LaskaKit/LED_Czech_Map/img/9.jpg

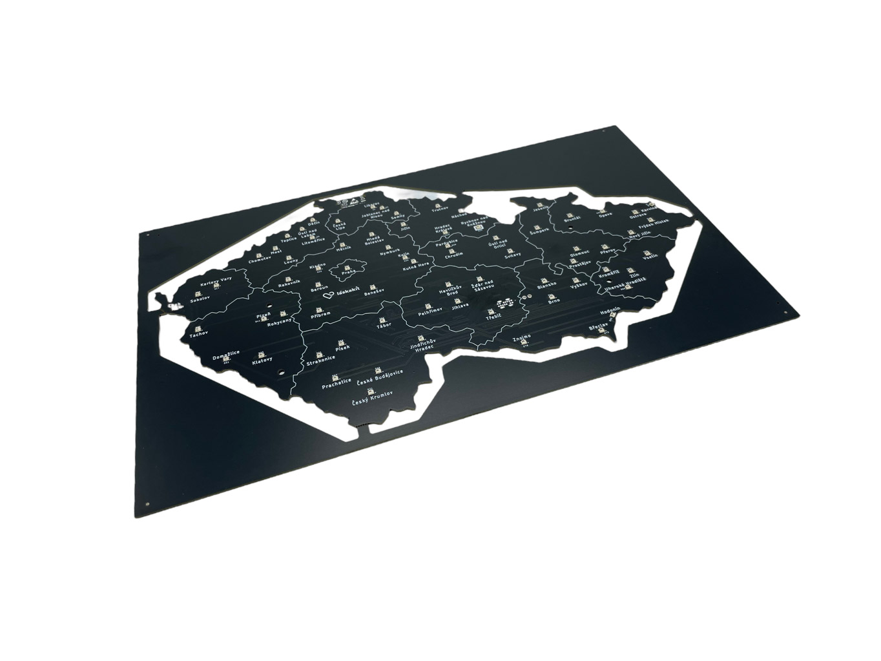
img/9.jpg
