LaskaKit/LED_Czech_Map/img/11.jpg

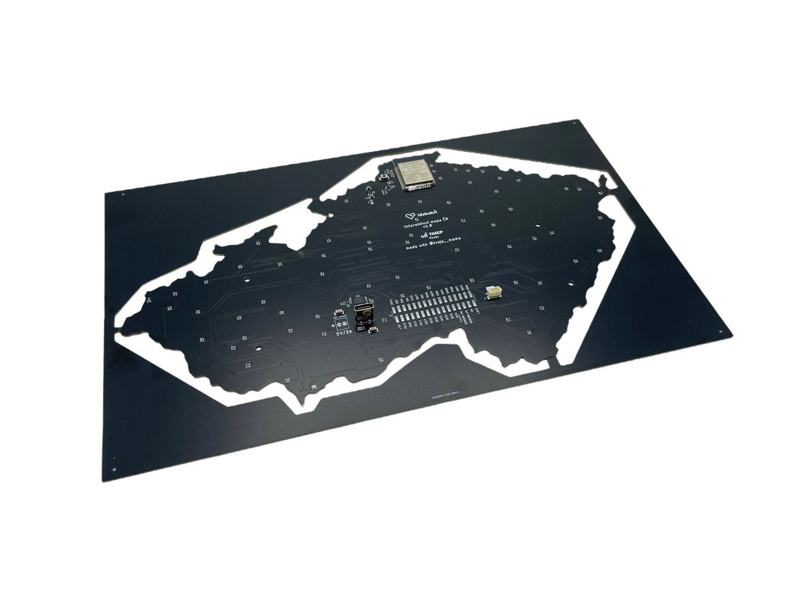
img/11.jpg
