LaskaKit/LED_Czech_Map/SW/Hra_Zachran_Mesto/laskakit_mapa_kontrola_otazek.png

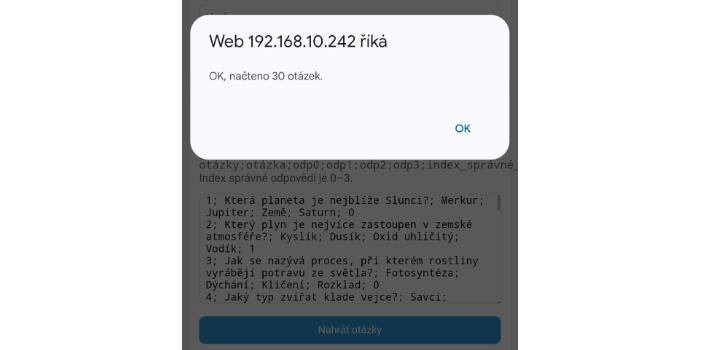
SW/Hra_Zachran_Mesto/laskakit_mapa_kontrola_otazek.png
