LaskaKit/LED_Czech_Map/SW/Hra_Zachran_Mesto/laskakit_mapa_uhasene_mesto.png

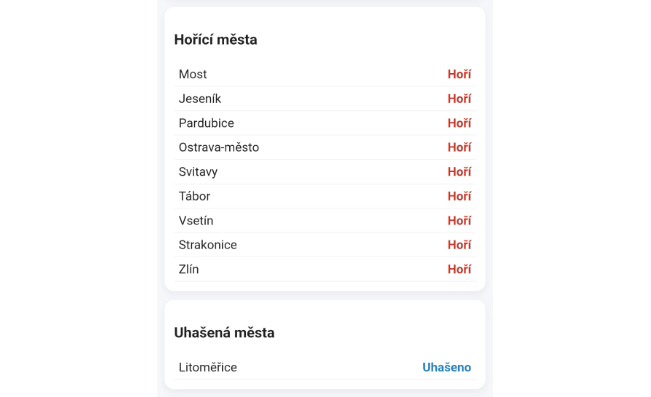
SW/Hra_Zachran_Mesto/laskakit_mapa_uhasene_mesto.png
